Achicken7301/farm-security/esp32-firmware-for-cam/main/include/main.h

#ifndef __MAIN_H__
#define __MAIN_H__
#include <driver/timer.h>
#include <nvs_flash.h>

#include "fsm_hc_501.h"
#include "fsm_ir_led.h"
#include "fsm_power_save.h"
#include "global.h"
#include "sch_task.h"
#include "scheduler.h"

#define CPU_CLOCK 80

#if USE_CAMERA
#include "fsm_camera.h"
#endif

#if USE_MESH
#include "fsm_mesh.h"
#endif

#if USE_TCP_SERVER
#include "fsm_ap.h"
#include "fsm_tcp_server.h"
#endif

#if USE_HTTP_CLIENT
#include "fsm_http_client.h"
#include "fsm_sta.h"
#endif

#if USE_HTTP_SERVER
#include "fsm_ap.h"
#include "fsm_http_server.h"
#endif

#endif // End #ifndef __MAIN_H__
