Achicken7301/farm-security/esp32-firmware-for-cam/main/fsm_power_save.c

#include "fsm_power_save.h"
PowerSaveState psState = POWER_SAVE_INIT;
const char *POWER_SAVE_TAG = "POWER SAVE";

const int ext_wakeup_pin_0 = HC501_PIN;

void startDeepSleep() { set_psState(POWER_SAVE_START); }
void deep_sleep_wakeup_by_gpio() { set_psState(POWER_SAVE_GPIO_WAKEUP_CONFIG); }
void deep_sleep_wakeup_by_timer()
{
  // ESP_LOGE(POWER_SAVE_TAG, "Start deep sleep setup");
  set_psState(POWER_SAVE_TIMER_WAKEUP_CONFIG);
  SCH_Add(deep_sleep_wakeup_by_gpio, 500, ONCE);
  SCH_Add(startDeepSleep, 1000, ONCE);
}

char *get_psState(PowerSaveState state)
{
  switch (state)
  {
  case POWER_SAVE_INIT:
    return "POWER_SAVE_INIT";
  case POWER_SAVE_DEINIT:
    return "POWER_SAVE_DEINIT";
  case POWER_SAVE_GPIO_WAKEUP_CONFIG:
    return "POWER_SAVE_GPIO_WAKEUP_CONFIG";
  case POWER_SAVE_TIMER_WAKEUP_CONFIG:
    return "POWER_SAVE_TIMER_WAKEUP_CONFIG";
  case POWER_SAVE_DO_NOTHING:
    return "POWER_SAVE_DO_NOTHING";
  case POWER_SAVE_START:
    return "POWER_SAVE_START";
  default:
    return UNKNOWN_STATE;
  }
}

/**
 * @brief Set Power Save state
 *
 *
 * @param POWER_SAVE_INIT
 * @param POWER_SAVE_DEINIT
 * @param POWER_SAVE_DO_NOTHING
 */
void set_psState(PowerSaveState state)
{
  char *temp = get_psState(state);
  if (strcmp(temp, UNKNOWN_STATE))
  {
    ESP_LOGI(POWER_SAVE_TAG, "Current State %s", get_psState(state));
  }
  else
  {
    ESP_LOGI(POWER_SAVE_TAG, "Current State %d", (state));
  }

  psState = state;
}

void fsm_power_save()
{
  switch (psState)
  {
  case POWER_SAVE_INIT:
  {
    /* Wake up reason */
    switch (esp_sleep_get_wakeup_cause())
    {
    case ESP_SLEEP_WAKEUP_EXT0:
    {
      set_psState(POWER_SAVE_DEINIT);
      // DAY = 1;
      NIGHT = 1;
      // hc_501_gpio_init();

      /* Check fsm_hc_501 wakeup */
      // set_hc501State(HC501_FOUND);
    }
    break;
    case ESP_SLEEP_WAKEUP_TIMER:
    {
      // DAY = 0;
      NIGHT = 1;
      /* Only wake up from timer is at Night */
      ESP_LOGI(POWER_SAVE_TAG, "Wake up by timer");
      set_psState(POWER_SAVE_DO_NOTHING);
    }
    break;
    default:
      // SCH_Add(startDeepSleep, 10000, ONCE);
      set_psState(POWER_SAVE_DO_NOTHING);
      break;
    }
  }
  break;
  case POWER_SAVE_DEINIT:
  {
    rtc_gpio_deinit(ext_wakeup_pin_0);
    set_psState(POWER_SAVE_DO_NOTHING);
  }
  break;
  case POWER_SAVE_GPIO_WAKEUP_CONFIG:
  {
    ESP_LOGI(POWER_SAVE_TAG, "Enabling EXT0 wakeup on pin GPIO%d", ext_wakeup_pin_0);
    ESP_ERROR_CHECK(esp_sleep_enable_ext0_wakeup(ext_wakeup_pin_0, 1));

    // Configure pullup/downs via RTCIO to tie wakeup pins to inactive level during
    // deepsleep. EXT0 resides in the same power domain (RTC_PERIPH) as the RTC IO
    // pullup/downs. No need to keep that power domain explicitly, unlike EXT1.
    ESP_ERROR_CHECK(rtc_gpio_pullup_dis(ext_wakeup_pin_0));
    ESP_ERROR_CHECK(rtc_gpio_pulldown_en(ext_wakeup_pin_0));

    // Isolate GPIO12 pin from external circuits. This is needed for modules
    // which have an external pull-up resistor on GPIO12 (such as ESP32-WROVER)
    // to minimize current consumption.
    rtc_gpio_isolate(GPIO_NUM_12);

    set_psState(POWER_SAVE_DO_NOTHING);
    break;
  }
  case POWER_SAVE_TIMER_WAKEUP_CONFIG:
  {
    // ESP_LOGI(POWER_SAVE_TAG, "Go to sleep, wake up after %dsecs",
    //          TIMER_WAKEUP_TIME_IN_SEC);
    ESP_ERROR_CHECK(esp_sleep_enable_timer_wakeup(TIMER_WAKEUP_TIME_IN_SEC * 1000000));
    set_psState(POWER_SAVE_DO_NOTHING);
    break;
  }
  case POWER_SAVE_START:
  {
    ESP_LOGI(POWER_SAVE_TAG, "Wifi/Mesh stops");
    esp_wifi_stop();
    esp_mesh_deinit();
    ESP_LOGI(POWER_SAVE_TAG, "Entering Deep Sleep mode");
    esp_deep_sleep_start();
    set_psState(POWER_SAVE_DO_NOTHING);
  }
  break;
  case POWER_SAVE_DO_NOTHING:
  {
  }
  break;
  default:
    break;
  }
}
