Achicken7301/farm-security/esp32-firmware-for-cam/main/fsm_sta.c

/**
 * @file fsm_sta.c
 * @author
 * @brief This file is used for root connect to router and access through the
 * internet by using tcp socket API.
 * @version 0.1
 * @date 2024-02-26
 *
 * @copyright Copyright (c) 2024
 *
 */

#include "fsm_sta.h"

/* Create socket, send to server */
char rx_buffer[128];
const char host_ip[] = HOST_IP_ADDR;
int addr_family = 0;
struct sockaddr_in dest_addr;
int ip_protocol = 0;
int err;
int sock = -1;

wifi_config_t sta_config = {
    .sta =
        {
            .threshold.authmode = WIFI_AUTH_WPA_WPA2_PSK,
            .sae_pwe_h2e = WPA3_SAE_PWE_BOTH,
        },
};

/**
 * @brief This function config esp connects to router
 *
 */
void fsm_sta()
{
  switch (mState)
  {
  case MESH_STA_INTERFACE:
  {

#if USE_HTTP_SERVER || USE_TCP_SERVER
    if (!is_router_config())
    {
      break;
    }
#endif
    /* Start config Station Interface */
    ESP_LOGI(MESH_TAG, "Start TCP/IP configuration");
    esp_netif_create_default_wifi_sta();
    ESP_ERROR_CHECK(esp_wifi_set_mode(WIFI_MODE_STA));
    memcpy(sta_config.sta.ssid, ROUTER_SSID, sizeof(ROUTER_SSID));
    memcpy(sta_config.sta.password, ROUTER_PASS, sizeof(ROUTER_PASS));
    ESP_ERROR_CHECK(esp_event_handler_instance_register(IP_EVENT, IP_EVENT_STA_GOT_IP,
                                                        &ip_event_handler, NULL, NULL));

    ESP_ERROR_CHECK(esp_wifi_set_config(WIFI_IF_STA, &sta_config));

    /*  register IP events handler */
    ESP_ERROR_CHECK(esp_wifi_set_storage(WIFI_STORAGE_FLASH));
    ESP_ERROR_CHECK(esp_wifi_start());
    ESP_ERROR_CHECK(esp_wifi_connect());

#if USE_MESH
    set_mState(MESH_INIT);
#elif USE_HTTP_CLIENT
    set_mState(MESH_DO_NOTHING);
    set_hcState(HTTP_CLIENT_INIT);
#else
    set_mState(MESH_DO_NOTHING);
#endif
  }
  break;
  case MESH_SOCKET_INIT:
  {
    if (sock != -1)
    {
      ESP_LOGI(MESH_TAG, "Socket is all ready init %d", sock);
      set_mState(MESH_SOCKET_SEND);
      break;
    }

    dest_addr.sin_addr.s_addr = inet_addr(host_ip);
    dest_addr.sin_family = AF_INET;
    dest_addr.sin_port = htons(PORT);
    addr_family = AF_INET;
    ip_protocol = IPPROTO_IP;

    sock = socket(addr_family, SOCK_STREAM, ip_protocol);
    if (sock < 0)
    {
      ESP_LOGE(MESH_TAG, "Unable to create socket: errno %d", errno);
      break;
    }

    ESP_LOGI(MESH_TAG, "Socket created, connecting to %s:%d", host_ip, PORT);

    err = connect(sock, (struct sockaddr *)&dest_addr, sizeof(struct sockaddr_in6));

    if (err != 0)
    {
      ESP_LOGE(MESH_TAG, "Socket unable to connect: errno %d", errno);
      set_mState(MESH_SOCKET_CLOSE);
      break;
    }
    ESP_LOGI(MESH_TAG, "Successfully connected");
    set_mState(MESH_SOCKET_SEND);
  }
  break;
  case MESH_SOCKET_SEND:
  {
    if (root_sendImage2server() == MESH_ROOT_SEND2SERVER_FAIL)
    {
      ESP_LOGE(MESH_TAG, "Error occurred during sending: errno %d", errno);
      set_mState(MESH_SOCKET_CLOSE);
      break;
    }

    ESP_LOGI(MESH_TAG, "Send success");
    /* Check if server reponse */
    // set_mState(MESH_SOCKET_RECEIVE);

    /* No need to response  */
    set_mState(MESH_SOCKET_CLOSE);
  }
  break;
  case MESH_SOCKET_RECEIVE:
  {
    /* Should switch to try_receive and set non-blocking */
    int len = recv(sock, rx_buffer, sizeof(rx_buffer) - 1, 0);
    // Error occurred during receiving
    if (len < 0)
    {
      set_mState(MESH_SOCKET_SEND);
      break;
    }
    // Data received
    else
    {
      rx_buffer[len] = 0; // Null-terminate whatever we received and treat
                          // like a string
      ESP_LOGI(MESH_TAG, "Received %d bytes from %s:", len, host_ip);
      ESP_LOGI(MESH_TAG, "%s", rx_buffer);

      /* process tcp receive here */
      if (process_server_data(rx_buffer) == TCP_MESH_OK)
      {
        ESP_LOGI(MESH_TAG, "Server receive message, closing socket");
        set_mState(MESH_SOCKET_CLOSE);
        break;
      }
    }
  }
  break;
  case MESH_SOCKET_CLOSE:
  {
    ESP_LOGE(MESH_TAG, "Shutting down socket and restarting...");
    shutdown(sock, 0);
    close(sock);
    sock = -1;

    set_cState(CAM_CLEAR_PIC);
    set_mState(MESH_DO_NOTHING);
  }
  break;
  default:
    break;
  }
}

/**
 * @brief Get global pic and send to server through tcp socket,
 * I'll explain ~the algorithm~ this later, not that hard.
 *
 */
MeshError_t root_sendImage2server()
{
  /* Send image bytes */
  char payload[50];
  // int file_size = sprintf(payload, "%zu", pic->len);
  int file_size = sprintf(payload, "%zu", pic->len);
  send(sock, payload, file_size, 0);

  int package = 0;
  for (package = 0; package < pic->len / TX_BUFF_MAX; package++)
  {
    err = send(sock, &pic->buf[package * (TX_BUFF_MAX)], TX_BUFF_MAX, 0);

    if (err < 0)
    {
      ESP_LOGE(FSM_CAMERA_TAG, "FAIL SENDING Erro: 0x%x", err);
      return MESH_ROOT_SEND2SERVER_FAIL;
    }
    /* Better check receive */
  }

  /* Send last package */
  int bytes_left = pic->len % TX_BUFF_MAX;
  err = send(sock, &pic->buf[package * TX_BUFF_MAX], bytes_left, 0);

  if (err < 0)
  {
    ESP_LOGE(FSM_CAMERA_TAG, "FAIL SENDING last package: %d, Erro: 0x%x", package, err);
    return MESH_ROOT_SEND2SERVER_FAIL;
  }
  printf("total package: %d\n", package);

  return MESH_ROOT_SEND2SERVER_SUCCESS;
}

void ip_event_handler(void *arg, esp_event_base_t event_base, int32_t event_id,
                      void *event_data)
{
  const char *IP_EVENT_HANDLER_TAG = "IP EVENT HANDLER";
  switch (event_id)
  {
  case IP_EVENT_STA_GOT_IP:
  {
    ip_event_got_ip_t *event = (ip_event_got_ip_t *)event_data;
    ESP_LOGI(IP_EVENT_HANDLER_TAG, "got ip:" IPSTR, IP2STR(&event->ip_info.ip));

    // set_cState(CAM_INIT);
  }
  break;
  default:
    ESP_LOGI(IP_EVENT_HANDLER_TAG, "event_base: %s\tevent_id%d", event_base, event_id);
    break;
  }
}
