Achicken7301/farm-security/esp32-firmware-for-cam/main/include/fsm_mesh.h

#ifndef __FSM_MESH_H__
#define __FSM_MESH_H__

#include <esp_err.h>
#include <esp_event.h>
#include <esp_log.h>
#include <esp_mac.h>
#include <esp_mesh.h>
#include <esp_mesh_internal.h>
#include <esp_wifi.h>
#include <nvs_flash.h>
#include <string.h>

#include "fsm_camera.h"
#include "global.h"
#include "sch_task.h"
#include "scheduler.h"

#if USE_HTTP_SERVER
#include "fsm_http_server.h"
#endif // End #ifdef USE_HTTP_SERVER

#define MESH_MAX_RX_BUFF 1024
#define MESH_MAX_TX_BUFF 1024

#define MESH_AP_CONNECTION 6

#define DUMP_DATA_BUFF 16 // 16 bytes per line
#define DUMP_DATA_LINES 4 // 4 lines * 16 bytes each

#define RE_SEND_IMAGE_INTERVAL 1000

typedef enum
{
  /* In-order to send message to external IP, root node need to config TCP/IP
   * on Station Interface
   * https://docs.espressif.com/projects/esp-idf/en/stable/esp32/api-guides/esp-wifi-mesh.html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.
   */
  MESH_STA_INTERFACE,
  /* Mesh from root send to server */
  MESH_SOCKET_INIT,
  MESH_SOCKET_SEND,
  MESH_SOCKET_RECEIVE,
  MESH_SOCKET_CLOSE,

  MESH_INIT,
  MESH_SEND_IMAGE, // Send header and command code to root
  MESH_RECEIVE,
  MESH_DO_NOTHING,
} MeshState;

extern int connected2Root;
extern MeshState mState;

void mesh_event_handler(void *event_handler_arg, esp_event_base_t event_base,
                        int32_t event_id, void *event_data);

void ip_event_handler(void *event_handler_arg, esp_event_base_t event_base,
                      int32_t event_id, void *event_data);
const char *get_mState();
void set_mState(MeshState);
void fsm_mesh();
#endif // End #ifndef __FSM_MESH_H__
