Achicken7301/farm-security/testing/esp32-esp8266-tcp/esp32-tcpserver/main/main.h

#ifndef __MAIN_H__
#define __MAIN_H__
#include "fsm_tcp_server.h"

#include <esp_err.h>
#include <esp_log.h>
#include <esp_netif.h>
#include <esp_wifi.h>
#include <nvs_flash.h>
extern int is_router_connected;
#define ROUTER_SSID "NHA"
#define ROUTER_PASS "0984012265"
#endif // End #ifndef __MAIN_H__
